Phil-dav/mailbox-lora-tracker/KiCAD/Images/Capture d’écran 2026-08-22 151105.png

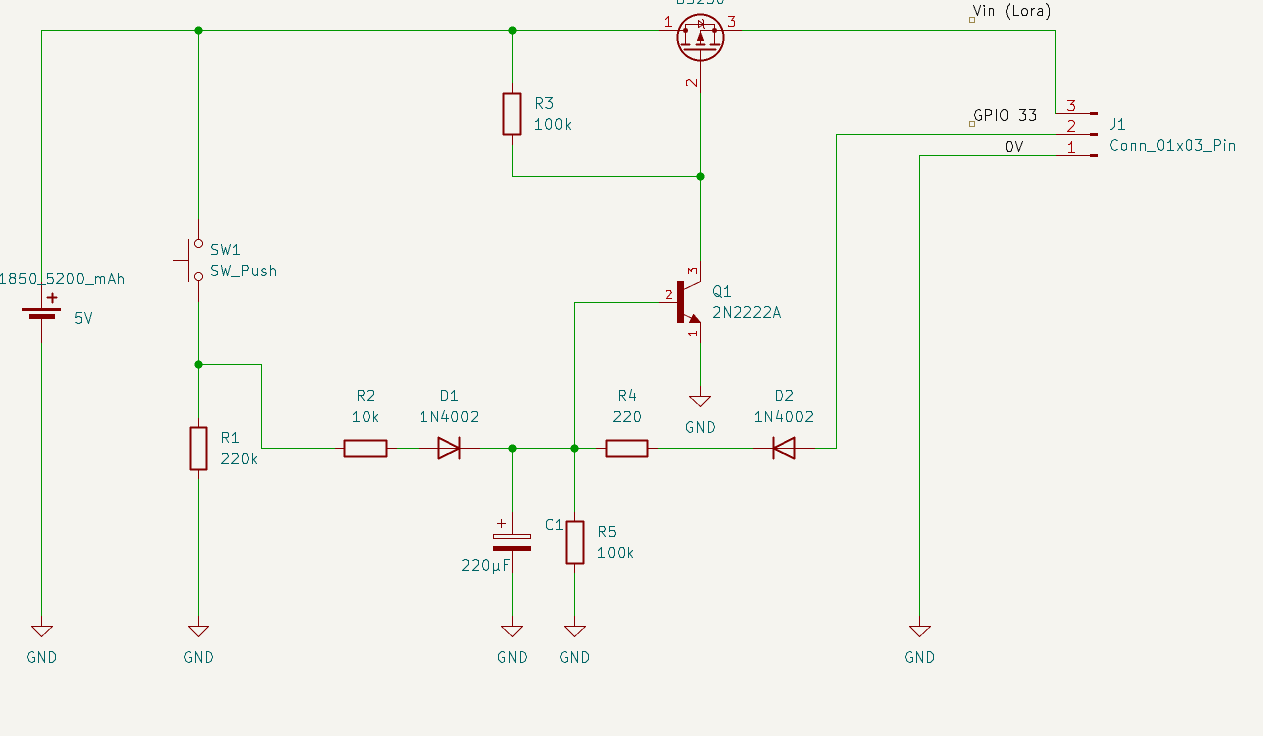
KiCAD/Images/Capture d’écran 2026-08-22 151105.png
