Phil-dav/mailbox-lora-tracker/KiCAD/Images/Latch MOSFET Lora final PCB.png

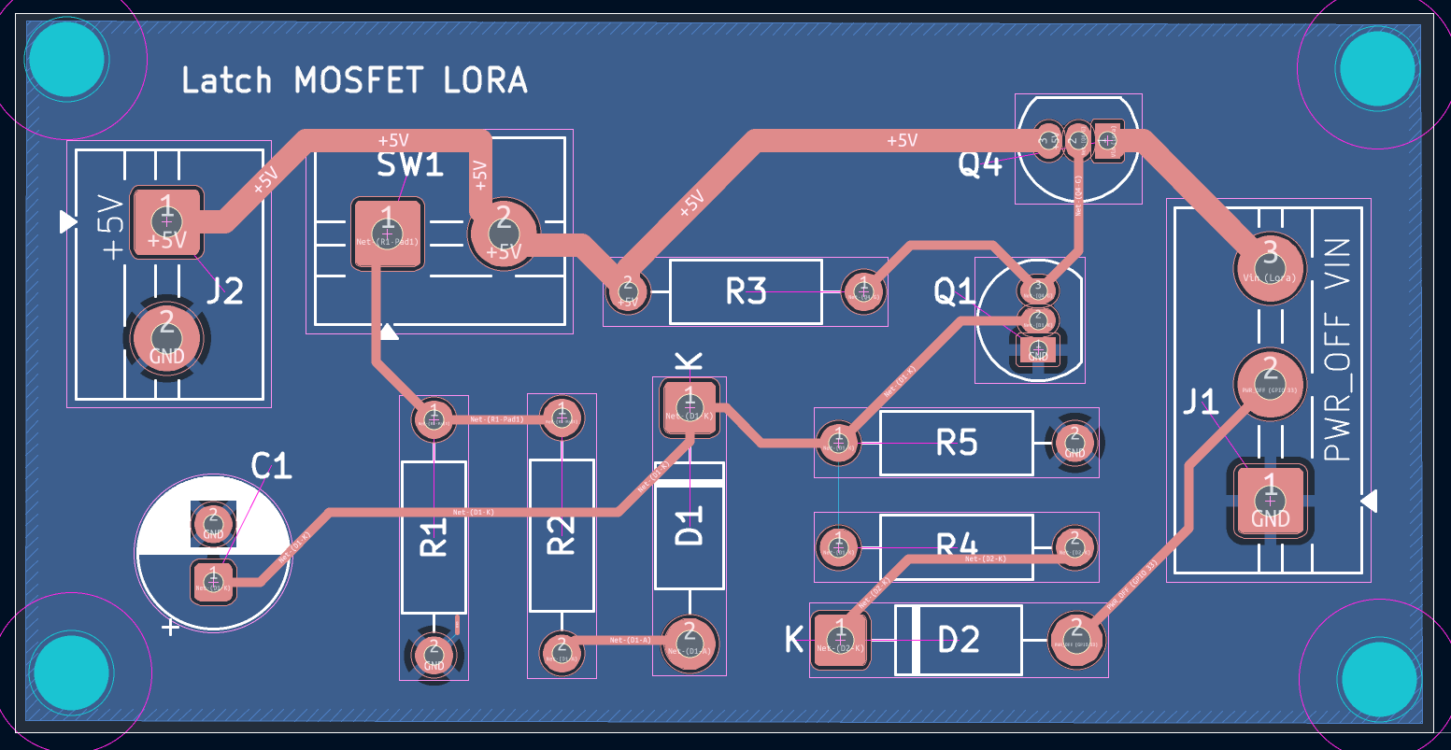
KiCAD/Images/Latch MOSFET Lora final PCB.png
