Phil-dav/mailbox-lora-tracker/KiCAD/Images/Latch MOSFET Lora RS.png

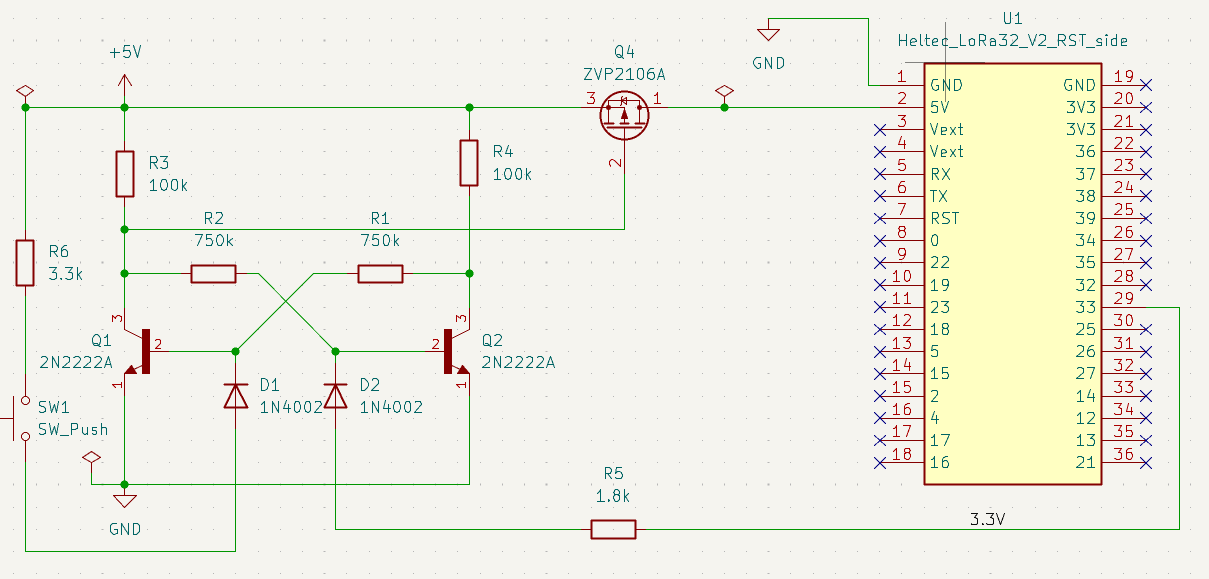
KiCAD/Images/Latch MOSFET Lora RS.png
