Phil-dav/mailbox-lora-tracker/KiCAD/Latch colis/FACE_CUIVRE_GRAVURE.png

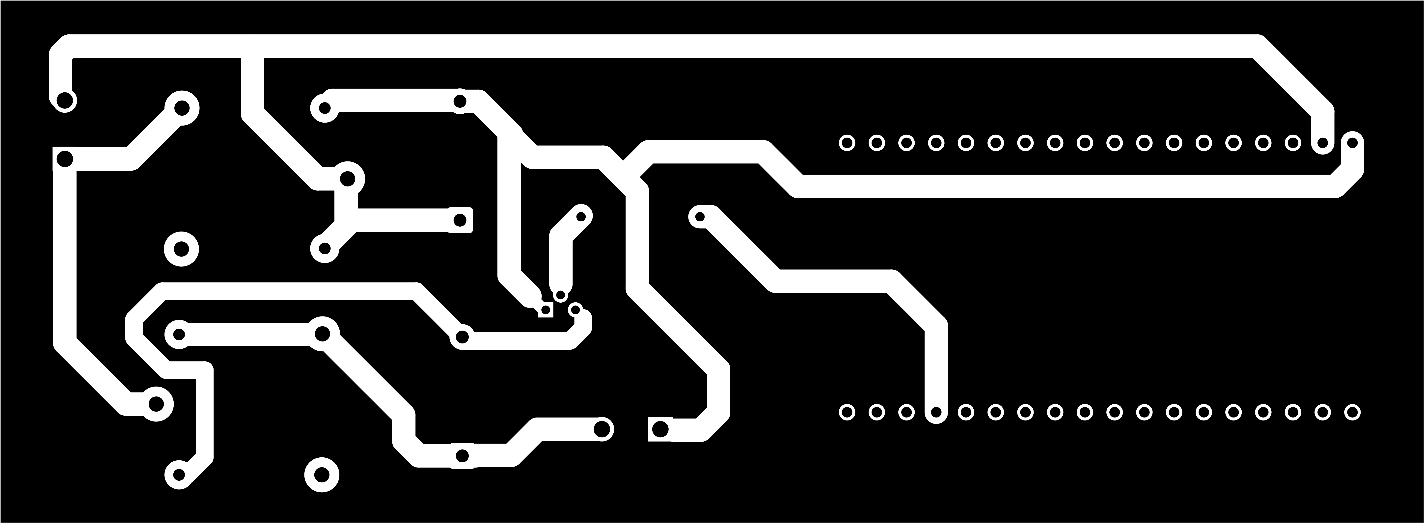
KiCAD/Latch colis/FACE_CUIVRE_GRAVURE.png
