Phil-dav/mailbox-lora-tracker/KiCAD/Latch colis/Gravure/composants_miroir.png

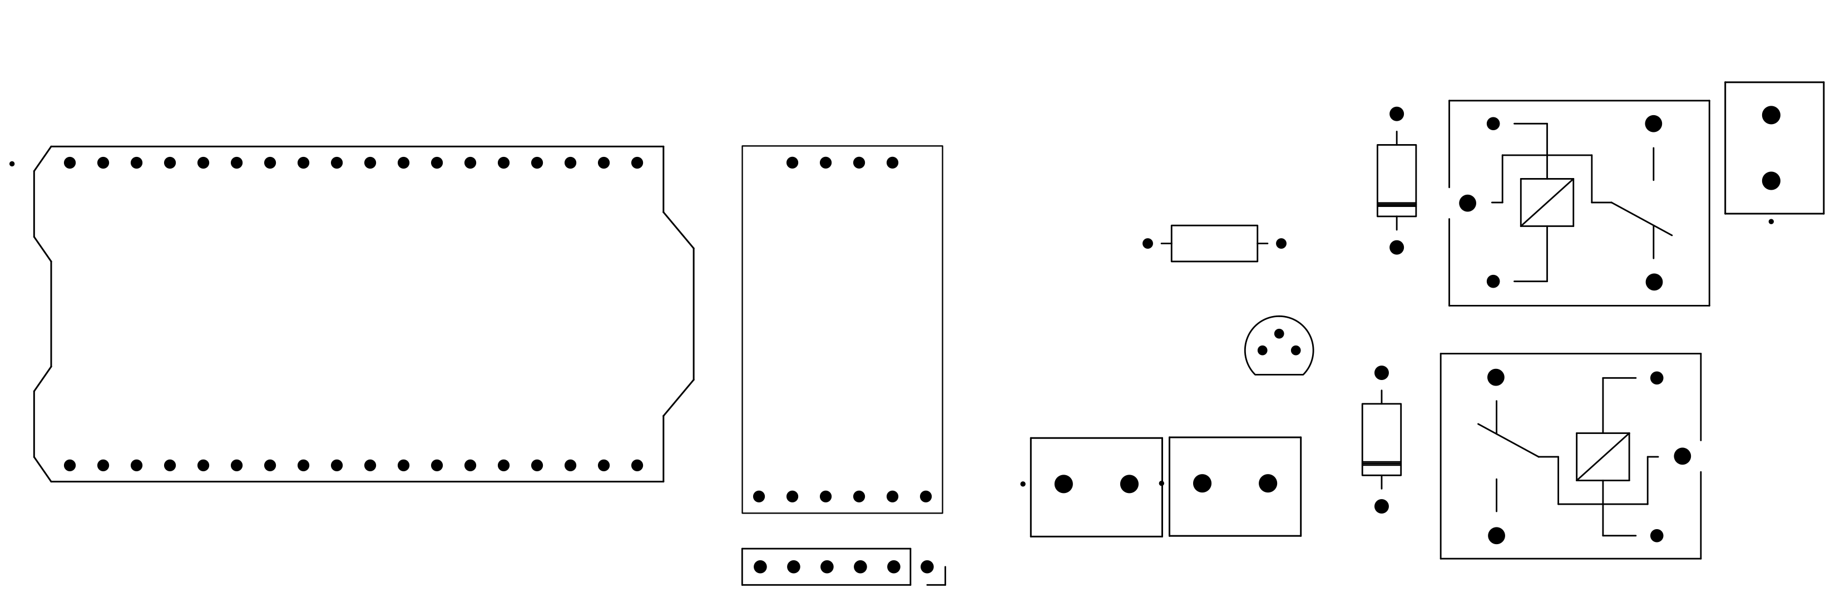
KiCAD/Latch colis/Gravure/composants_miroir.png
