Phil-dav/mailbox-lora-tracker/KiCAD/Latch colis/Gravure/cuivre_negatif.png

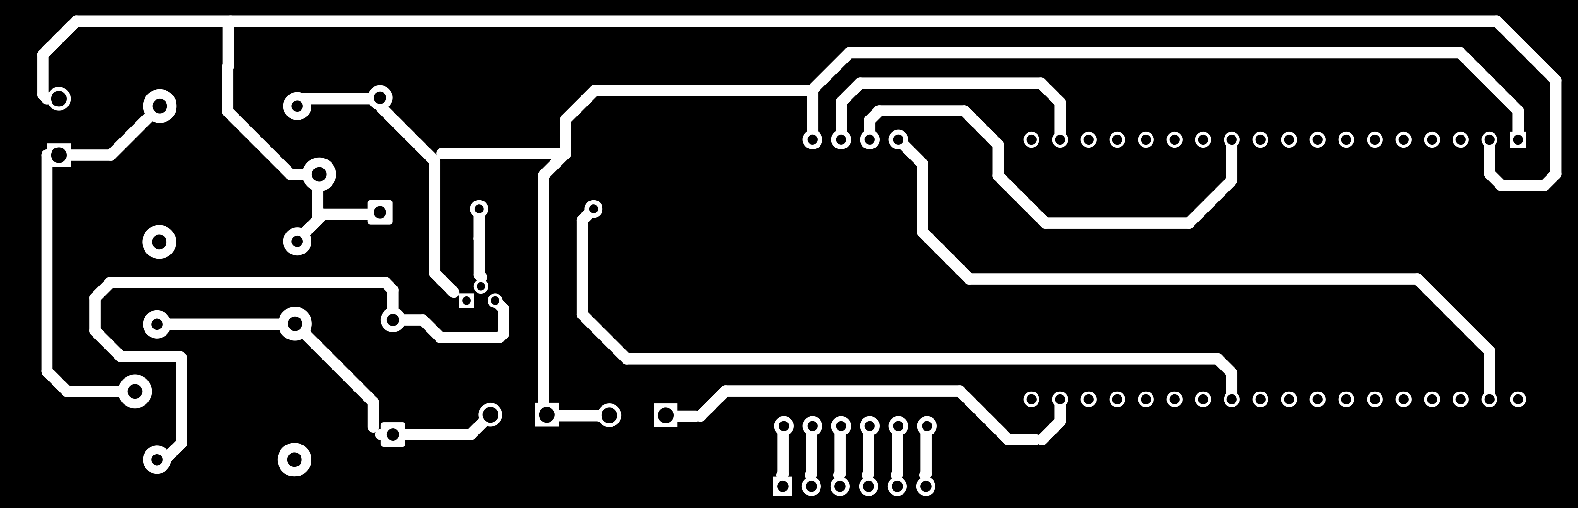
KiCAD/Latch colis/Gravure/cuivre_negatif.png
