Phil-dav/mailbox-lora-tracker/KiCAD/Latch colis/Gravure/cuivre_normal.png

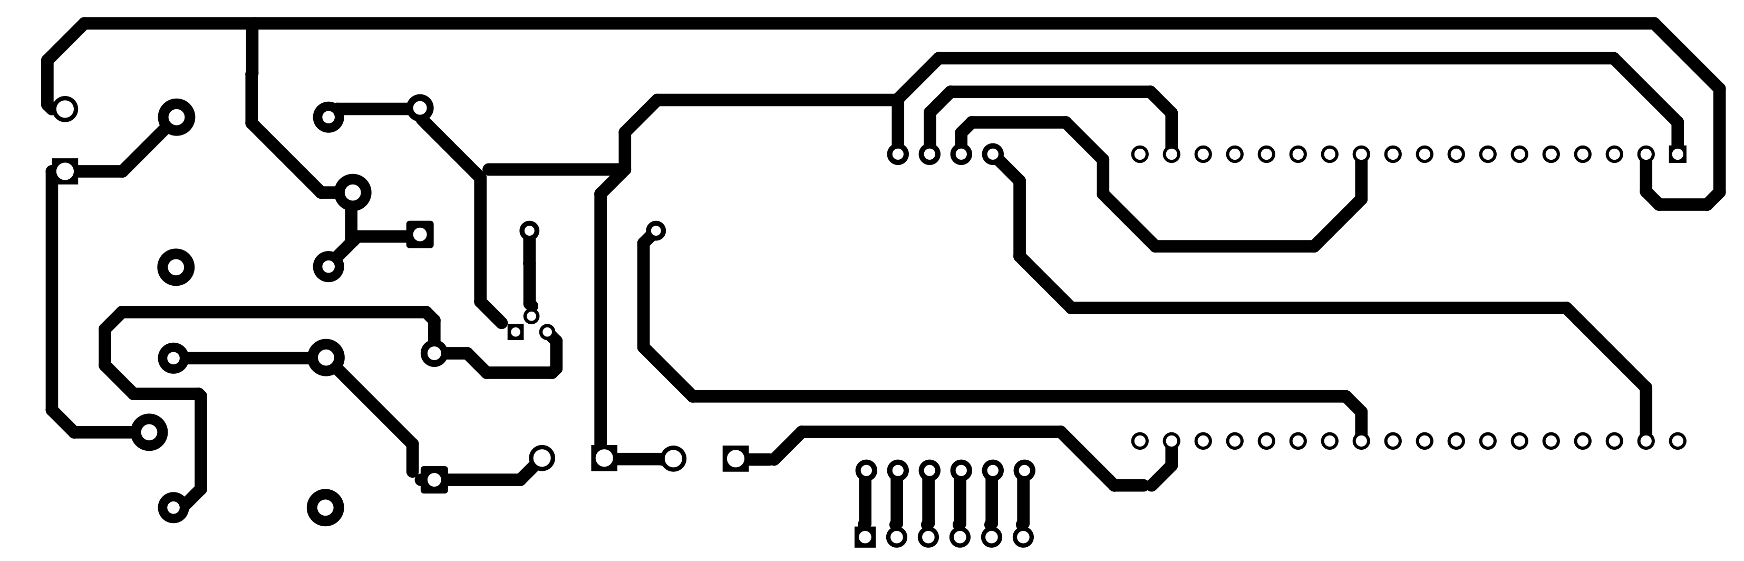
KiCAD/Latch colis/Gravure/cuivre_normal.png
