Phil-dav/mailbox-lora-tracker/KiCAD/Latch colis/Schema Lora Boîte aux lettres.png

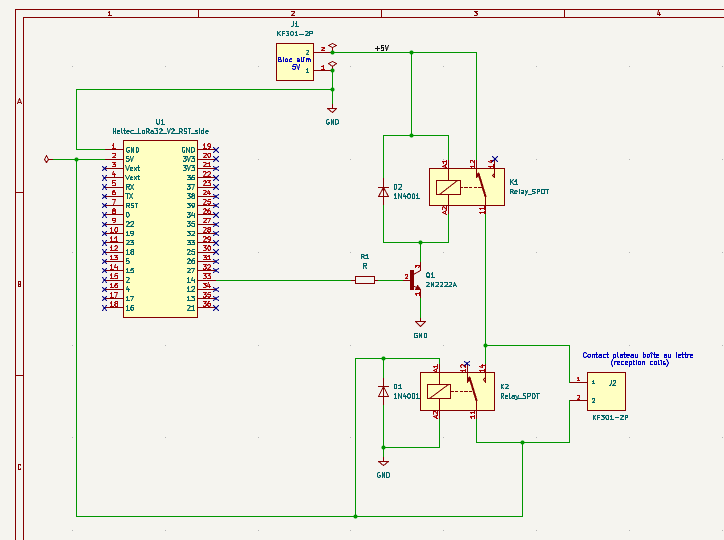
KiCAD/Latch colis/Schema Lora Boîte aux lettres.png
