Phil-dav/mailbox-lora-tracker/KiCAD/Latch colis/Schema.png

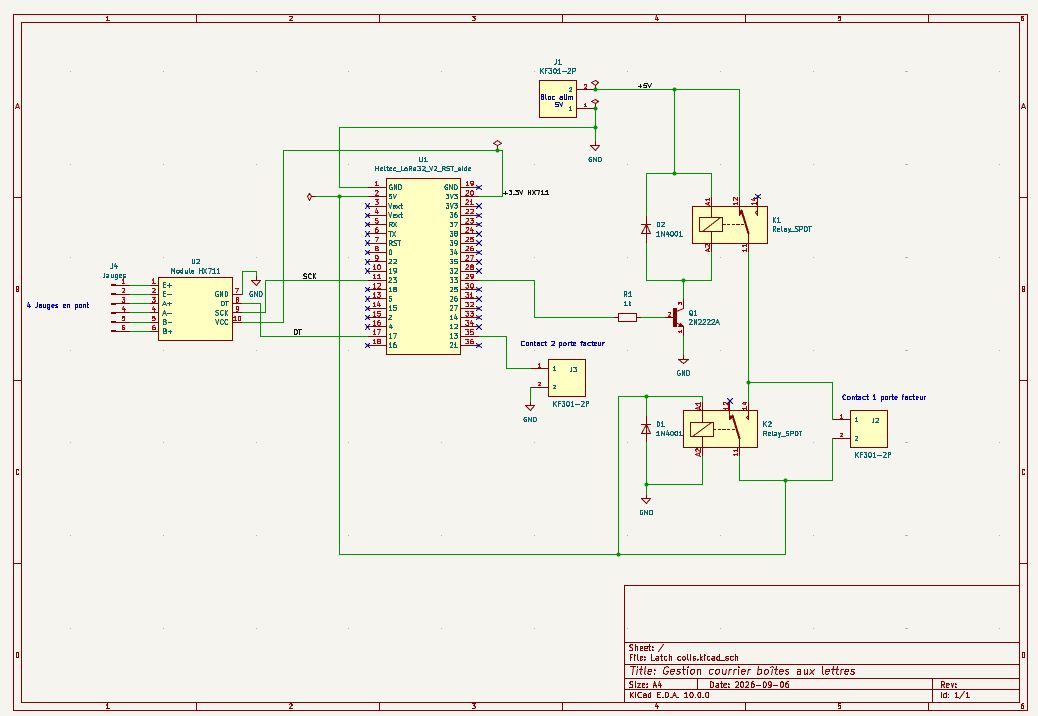
KiCAD/Latch colis/Schema.png
