Phil-dav/mailbox-lora-tracker/KiCAD/Latch colis/vue 3D avec HX711.png

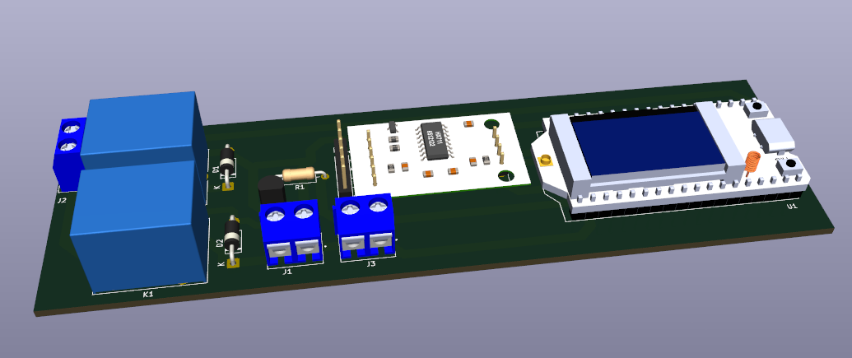
KiCAD/Latch colis/vue 3D avec HX711.png
