Phil-dav/mailbox-lora-tracker/KiCAD/Latch colis/Vue 3D Lora Boîte aux lettres.png

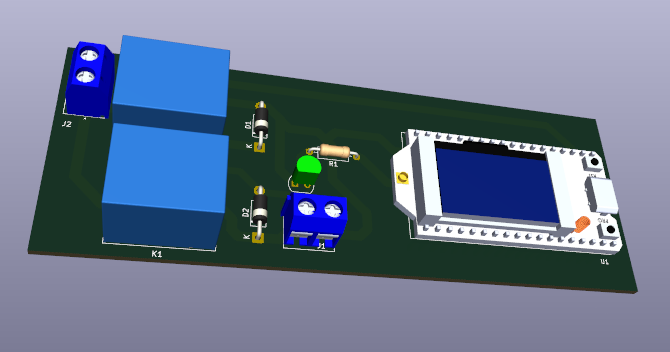
KiCAD/Latch colis/Vue 3D Lora Boîte aux lettres.png
