Phil-dav/mailbox-lora-tracker/KiCAD/latch_mosfet_boite_lettres/gerber_laser/latch_mosfet_boite_lettres_A_GRAVER.png

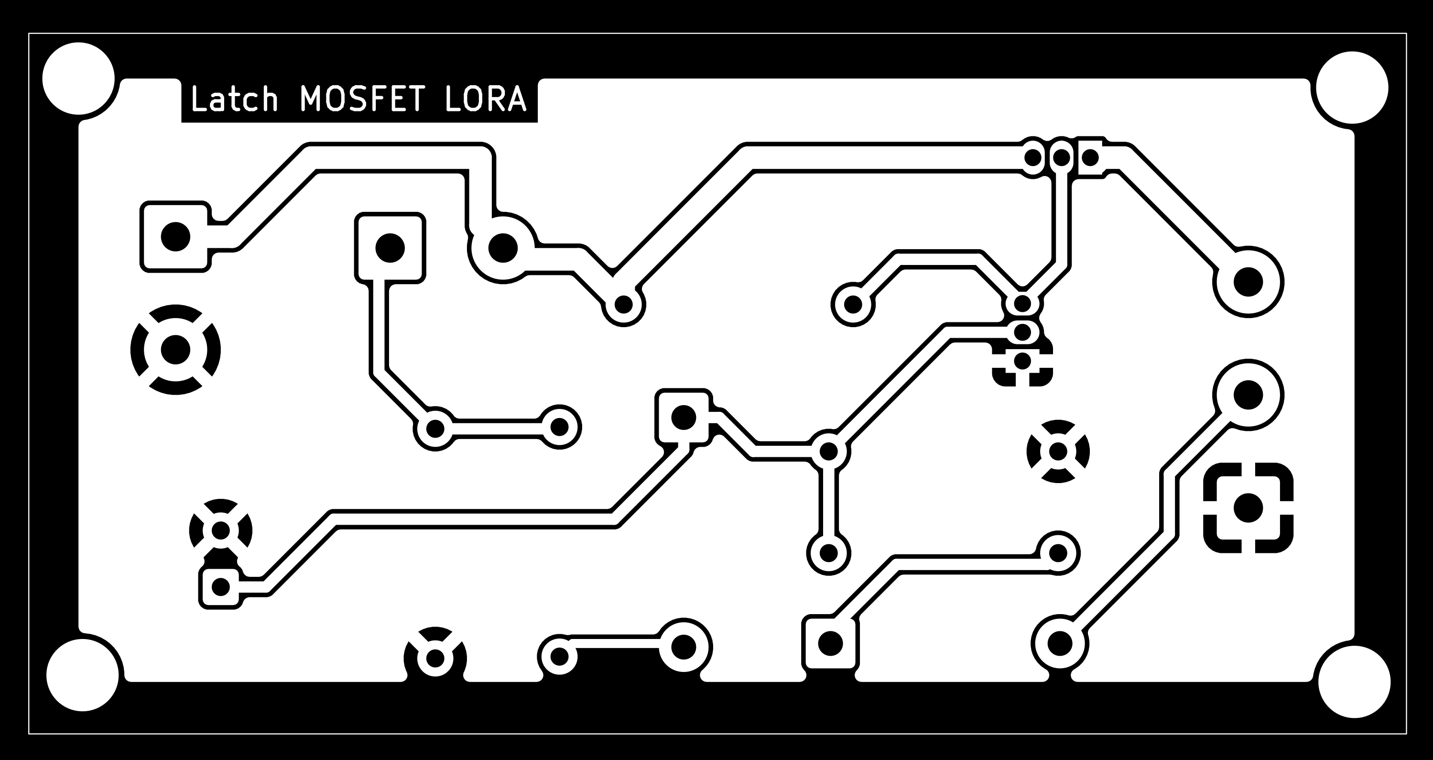
KiCAD/latch_mosfet_boite_lettres/gerber_laser/latch_mosfet_boite_lettres_A_GRAVER.png
