Phil-dav/mailbox-lora-tracker/KiCAD/latch_mosfet_boite_lettres_avec_lora/FACE_CUIVRE_GRAVURE.png

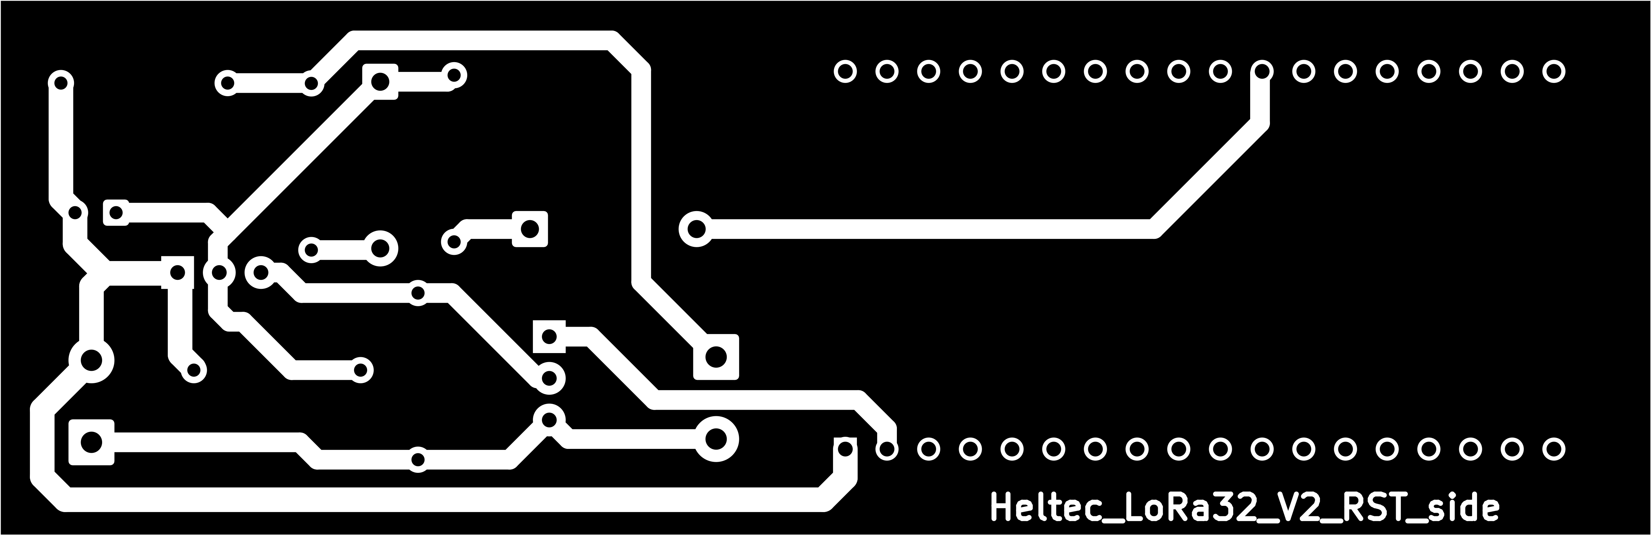
KiCAD/latch_mosfet_boite_lettres_avec_lora/FACE_CUIVRE_GRAVURE.png
