Phil-dav/mailbox-lora-tracker/KiCAD/latch_mosfet_boite_lettres_avec_lora/sauv/FACE_B_VERTICAL_FINAL.png

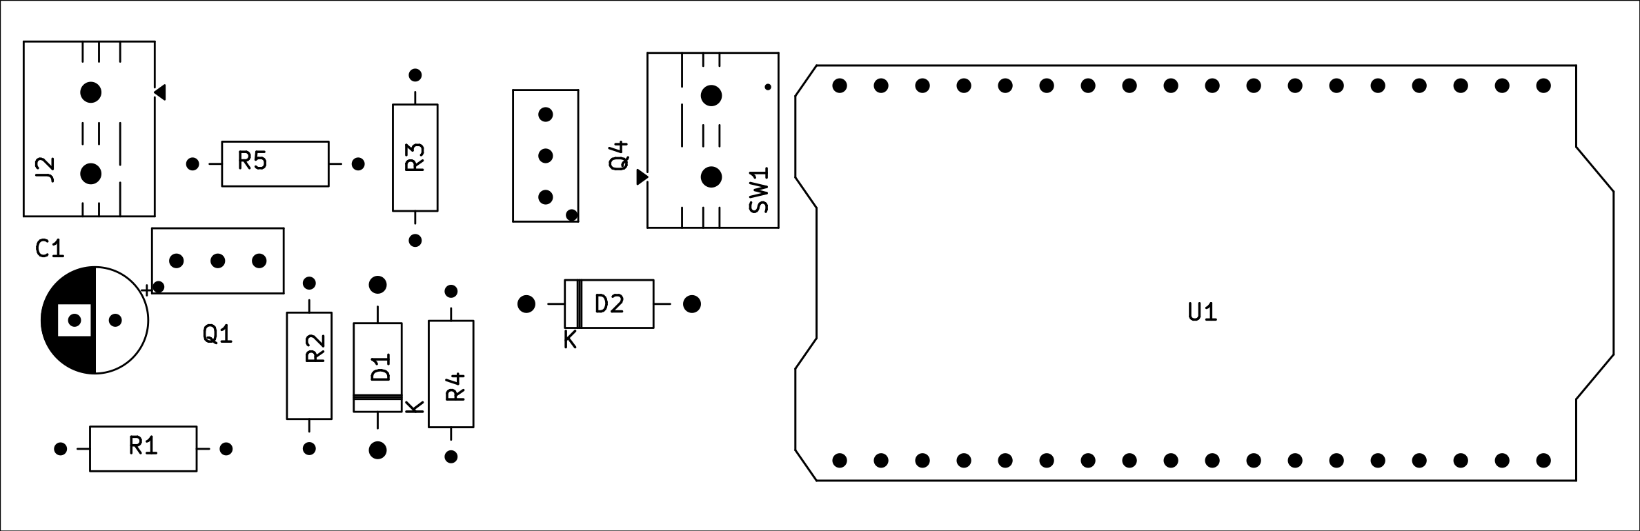
KiCAD/latch_mosfet_boite_lettres_avec_lora/sauv/FACE_B_VERTICAL_FINAL.png
